Grupo-4-ME4250-1-2025-2/Proyecto-Robot-Auto-Balancin/Diagramas/Diagrama de Flujo.png

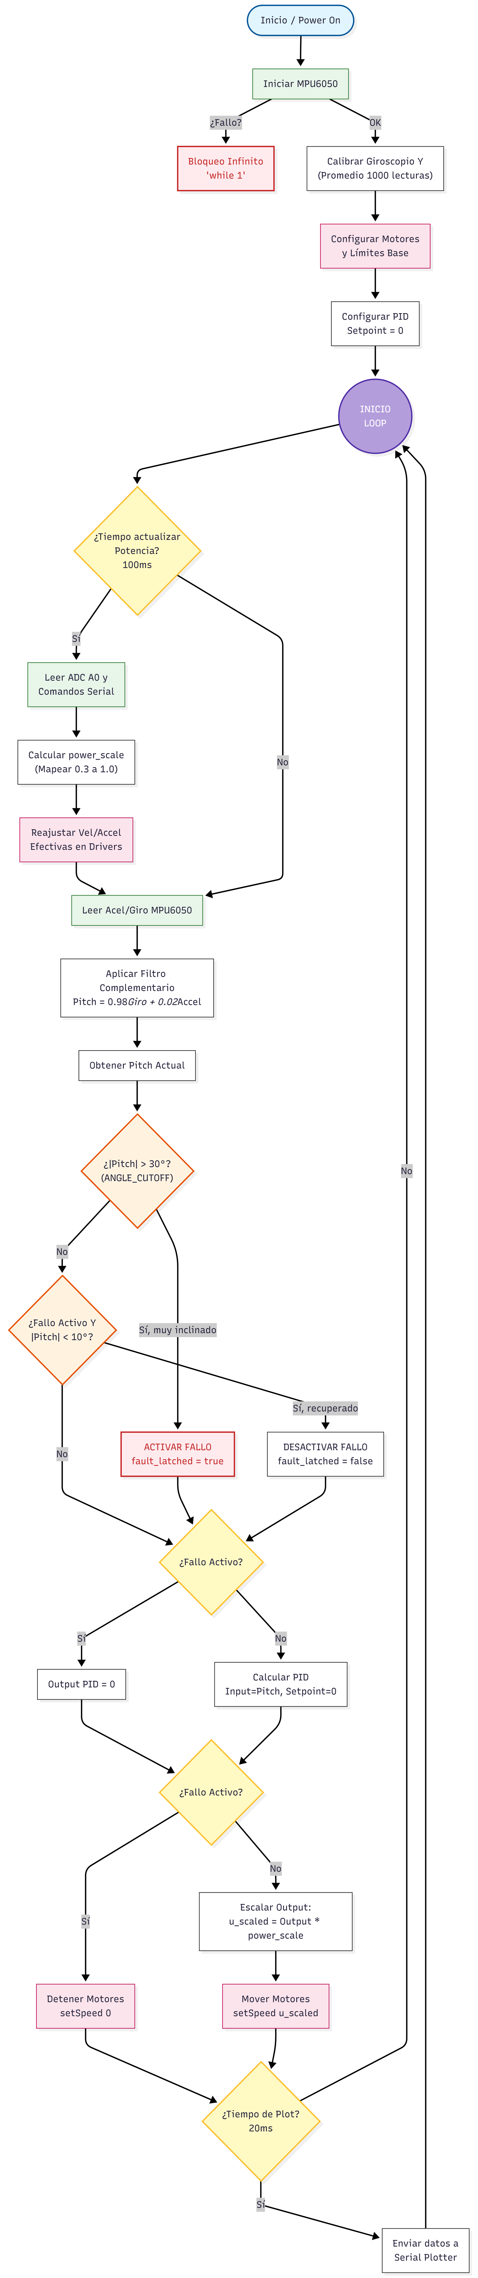
Diagramas/Diagrama de Flujo.png
