Grupo-4-ME4250-1-2025-2/Proyecto-Robot-Auto-Balancin/Registros/registro cabeza 1.jpeg

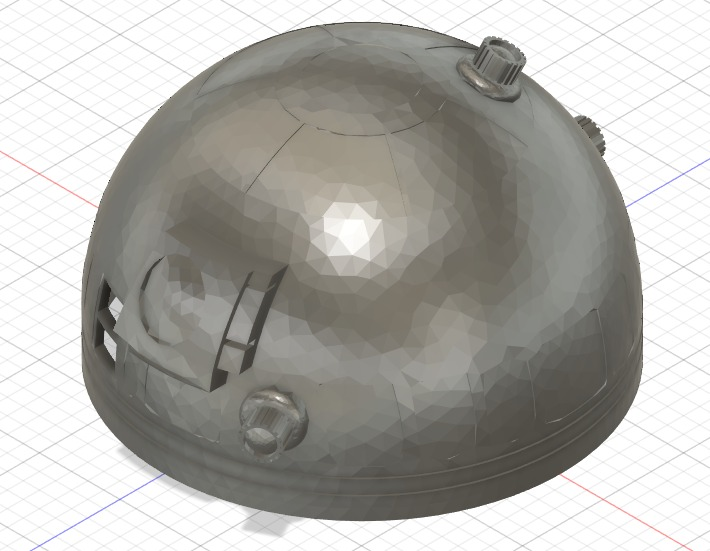
Registros/registro cabeza 1.jpeg
