Grupo-4-ME4250-1-2025-2/Proyecto-Robot-Auto-Balancin/Registros/soporte 2.jpeg

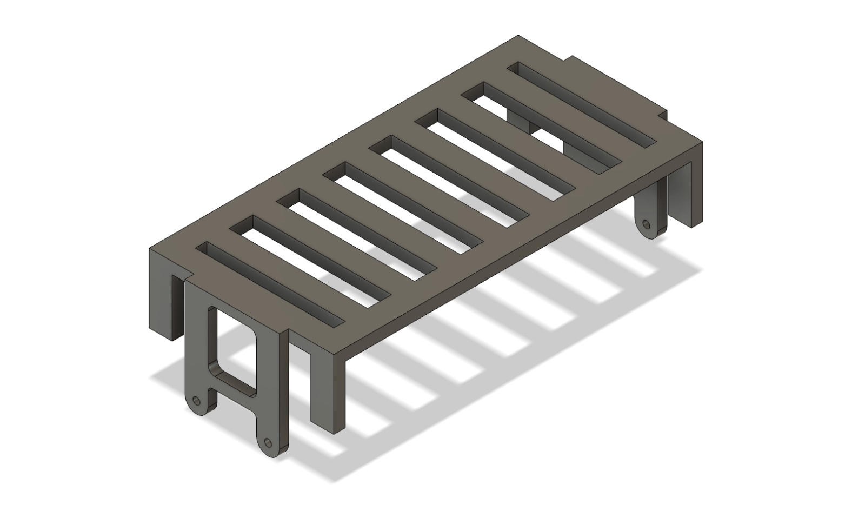
Registros/soporte 2.jpeg
